bkw777/Molex78802_Module/Carrier/pcb2molex8878_pin.stl

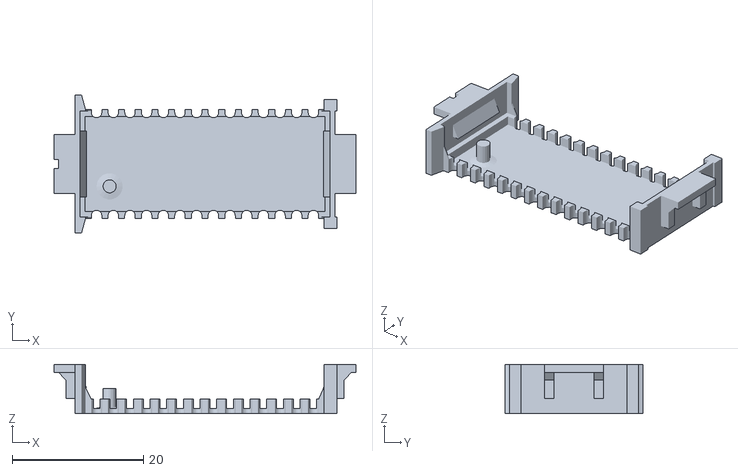
[picture p27: CAD file, 2020-02-29]
Carrier/pcb2molex8878_pin.stl
46.0 x 21.0 x 7.48
