bkw777/Molex78802_Module/Carrier/pcb2molex8878_max.stl

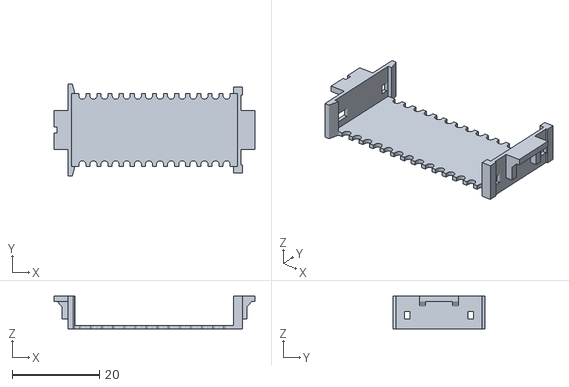
[picture p28: CAD file, 2020-02-29]
Carrier/pcb2molex8878_max.stl
46.0 x 21.0 x 7.48
